NET-BYU/sss/docs/assets/feet-sss.3mf

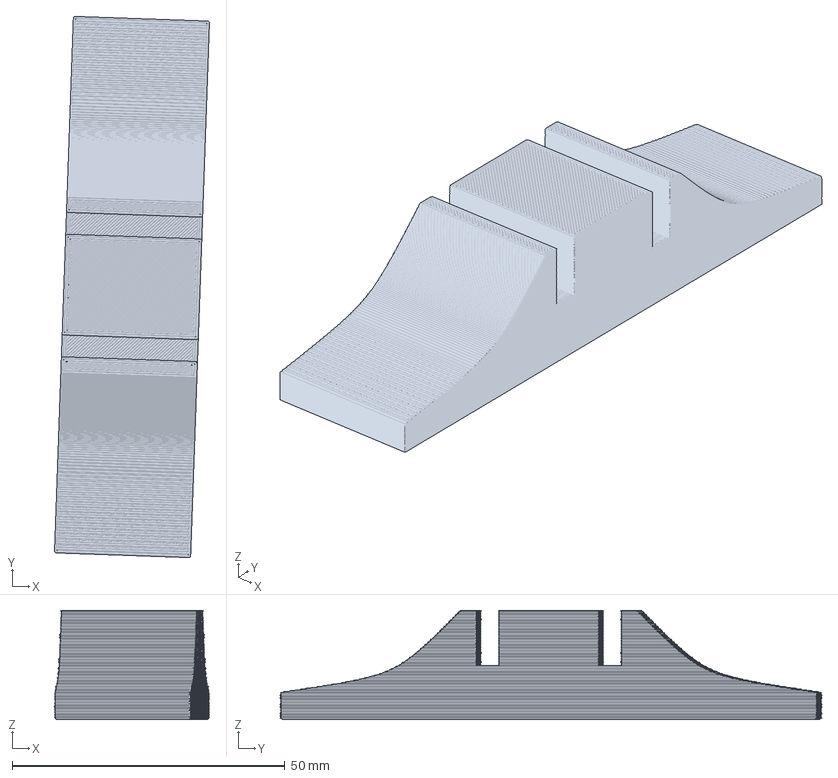
[picture p32: CAD file, 2022-08-18]
docs/assets/feet-sss.3mf
28.4 x 99.3 x 20.0 mm
