NET-BYU/sss/hw/case/10 Series/TS20-50-635 v5.3mf

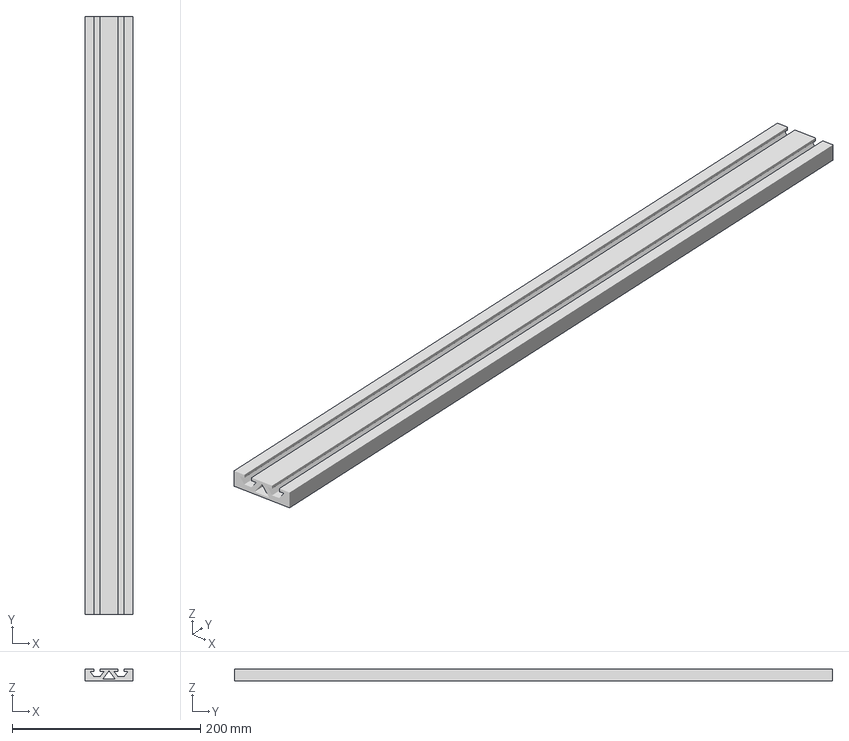
[picture p33: CAD file, 2024-08-19]
hw/case/10 Series/TS20-50-635 v5.3mf
50.8 x 635.4 x 12.7 mm
