NET-BYU/sss/hw/case/Brackets/Panel Holder 1 v4.3mf

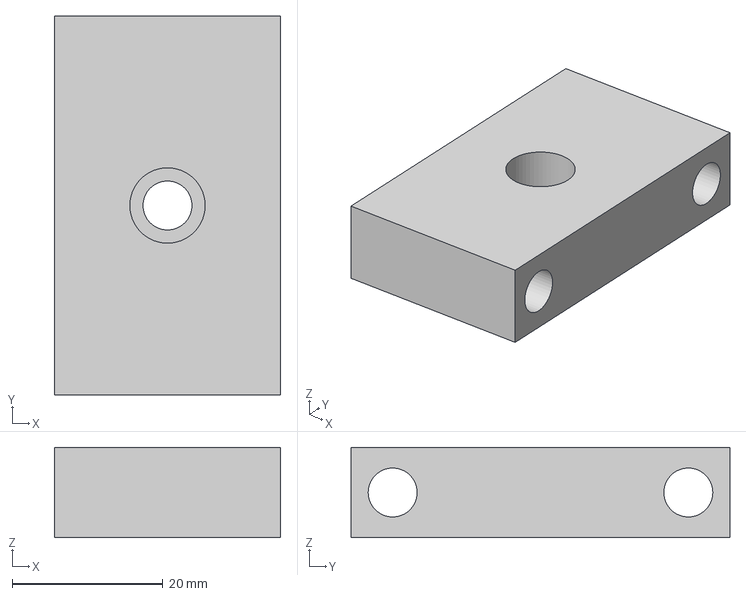
[picture p34: CAD file, 2024-08-19]
hw/case/Brackets/Panel Holder 1 v4.3mf
30.0 x 50.2 x 12.0 mm
