NET-BYU/sss/hw/case/Brackets/Big Bracket v3.3mf

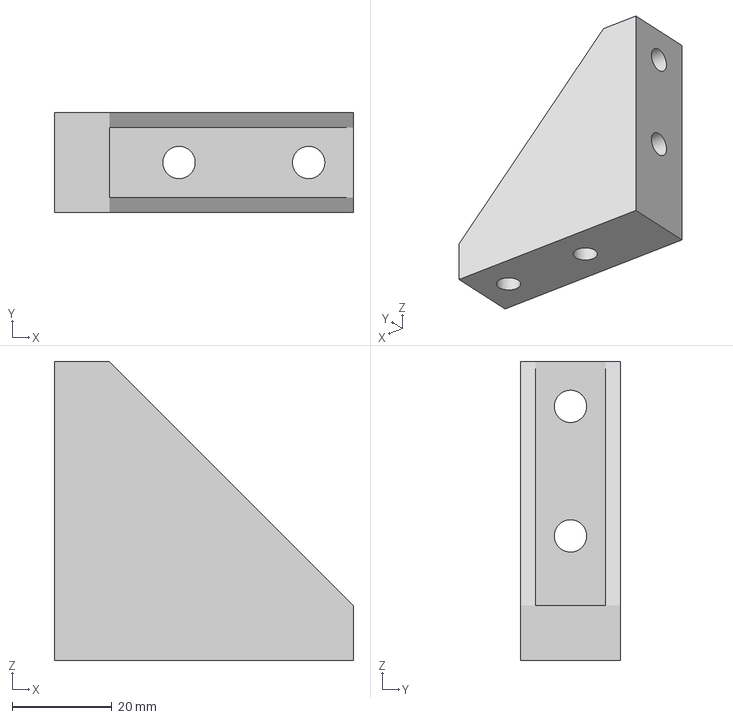
[picture p35: CAD file, 2024-08-19]
hw/case/Brackets/Big Bracket v3.3mf
60.0 x 20.0 x 60.0 mm
