NET-BYU/sss/hw/case/Brackets/Panel Holder 2 v2.3mf

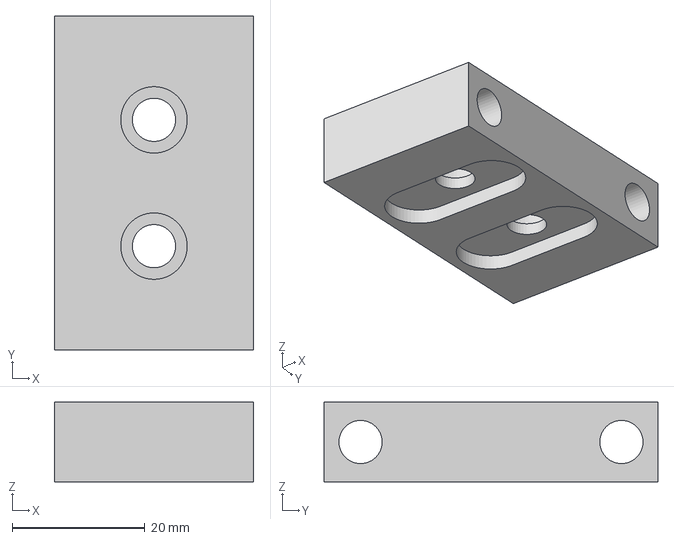
[picture p36: CAD file, 2024-08-19]
hw/case/Brackets/Panel Holder 2 v2.3mf
30.0 x 50.2 x 12.0 mm
