NET-BYU/sss/hw/case/Brackets/Spacer 2 v6.3mf

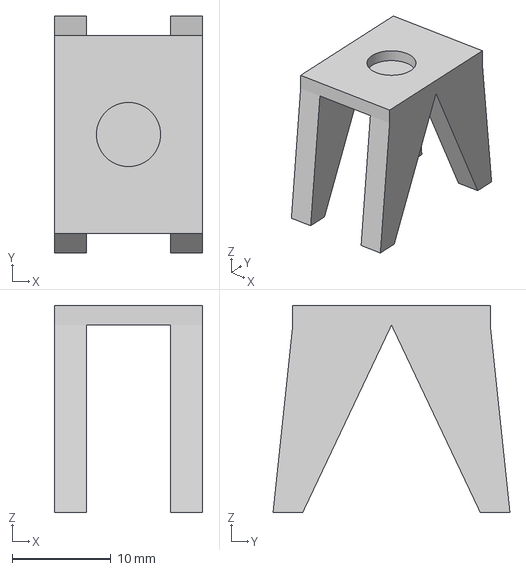
[picture p37: CAD file, 2024-08-19]
hw/case/Brackets/Spacer 2 v6.3mf
15.0 x 24.0 x 21.0 mm
